troisiemetype/teensymoog/misc/pictures/3.jpg

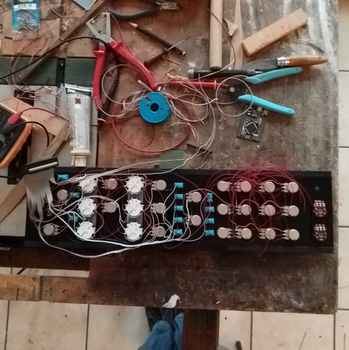
misc/pictures/3.jpg
