troisiemetype/teensymoog/misc/pictures/4.jpg

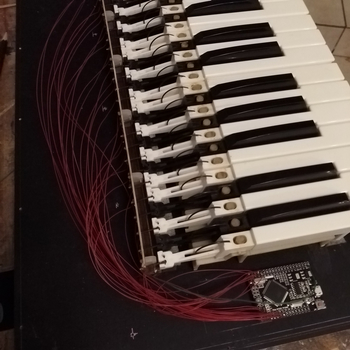
misc/pictures/4.jpg
